PatrickOrjieh/life-sync/Sprint_1/Optiband.pptx

## Optiband

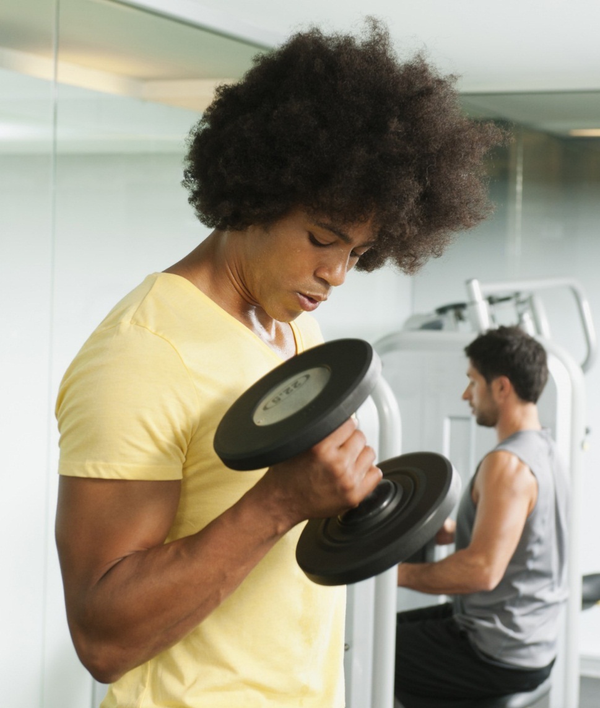
[picture p24: figure]
Two people lifting weights
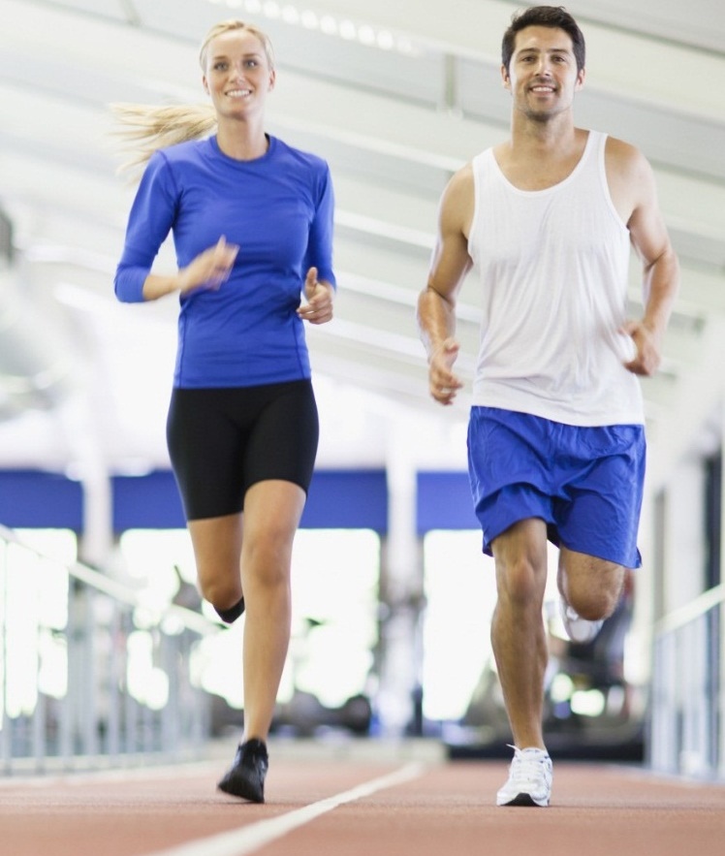
[picture p25: figure]
Man and woman running on indoor track

By LifeSync

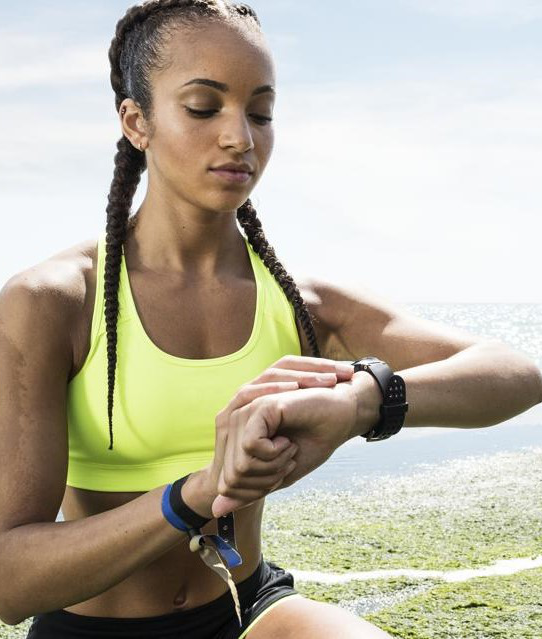
[picture p26: figure]

## Project Scope

- Develop a wearable fitness tracker
- Aid in achievement of optimal exercise
- Monitor user stats to provide guidance
- Avoidance of overexertion
- For teenagers/young adults new to the gym

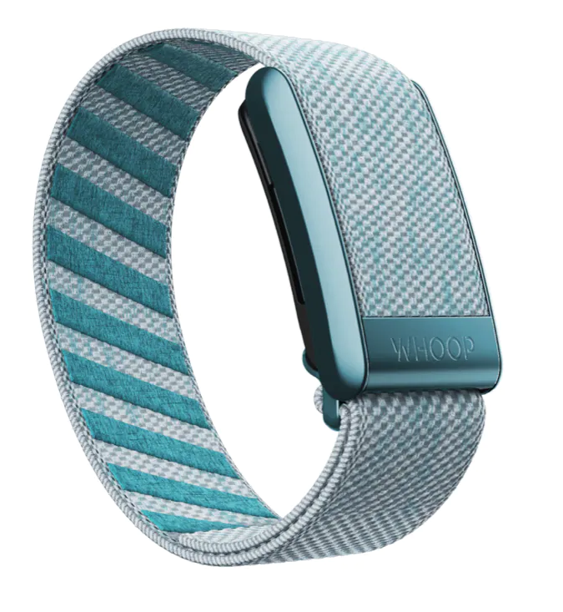
[picture p27: figure]

## Hardware Overview

- Insert Hardware info here

## Functional & Non-functional Requirements

Functional:
- Heart rate and Oxygen Saturation monitoring
- User Data Input
- Real-Time Feedback
- Workout Duration Timer
- Connectivity with Mobile App

Non-Functional:
Usability
Battery Life
Durability & build
Data security & privacy
Responsiveness

## U/T/S/E Analysis – Average user

- User – Some gym experience, uses technology regularly
- Task – engage in effective workouts without over exhaustion
- System – Valuable workout assistant & safety device
- Environment – Local gym, distractions: other gym-goers

## System Conceptual model design

- Hardware Components – Sensors, Bluetooth module, Battery
- Software Components – Mobile App, Account Management, Data Storage, Notifications
- User Experience – UI Design, User Feedback

## Thanks for listening!
