PatrickOrjieh/life-sync/Sprint_2/Amended Roles.docx

Roles

Robert - Team lead, Front-end Developer

Patrick - Back-end Developer, Database Management

Hannah – Hardware Management, Front-end Developer

Conor – UI Designer, Lead Tester
