PatrickOrjieh/life-sync/Sprint_0/Project-Role.docx

Project Manager Responsibilities: The Project Manager takes charge of overseeing the entire project from start to finish. To ensure that every task is in line with the project's goals, efficiently manage budgets, set timelines, and serve as the main point of contact for all stakeholders. Assigned to: Robert.

Scrum Master Responsibilities: The Scrum Master plays an important role in guiding the team through the Agile framework. To coordinate sprint planning sessions, lead daily hurdles, and review the outcomes of each sprint to ensure efficiency. Assigned to: It's a team effort - everyone is engaged.

Hardware Engineer Responsibilities: The Hardware Engineer explores the tangible aspects of the band. The focus is on picking out the right sensors, ensuring they function as intended, and communicating with other team members to integrate these components. Assigned to: Hannah.

Frontend Developer Responsibilities: The Frontend Developer crafts the visible parts of the apps linked with the band. The goal is to make sure it's not only responsive but also user-centric, and that it perfectly matches the vision laid out by the UI/UX designer. Assigned to: Robert.

UI/UX Designer Responsibilities: The UI/UX Designer is the creative force behind the project, tasked with sketching out user-friendly and attractive interfaces for the related apps. To ensure users have a hassle-free experience and work side by side with the Frontend Developer to make their designs a reality. Assigned to: Conor.

Backend and Database Developer Responsibilities: This role is all about the backbone of the application. The Backend and Database Developer ensures smooth communication between the server and frontend. Apart from that, design, roll out, and oversee the database, keeping eye on data safety and consistency. Assigned to: Patrick.

Tester (QA Engineer) Responsibilities: The Tester, or QA Engineer, is the last line of defense before the product reaches users. The duty is to identify any glitches, report them, and conduct tests on both the software and hardware parts. Work hand in hand with the developers to troubleshoot any found issues. Assigned to: Tom.
