PatrickOrjieh/life-sync/Sprint_3/UI Mockups/login page.jpg

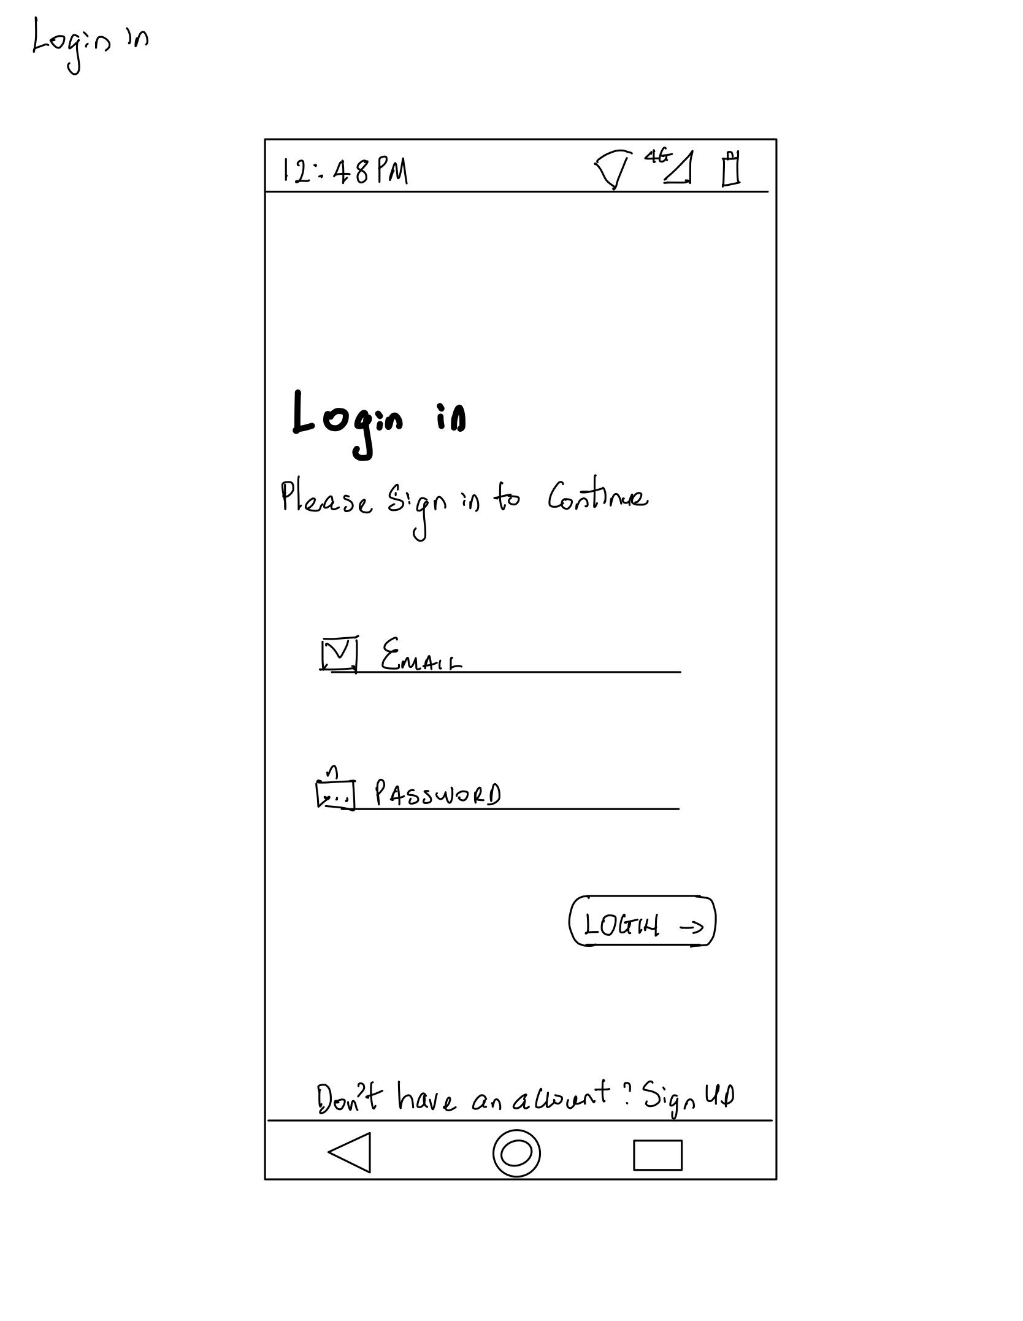
Sprint_3/UI Mockups/login page.jpg
