PatrickOrjieh/life-sync/Sprint_3/UI Mockups/main page.jpg

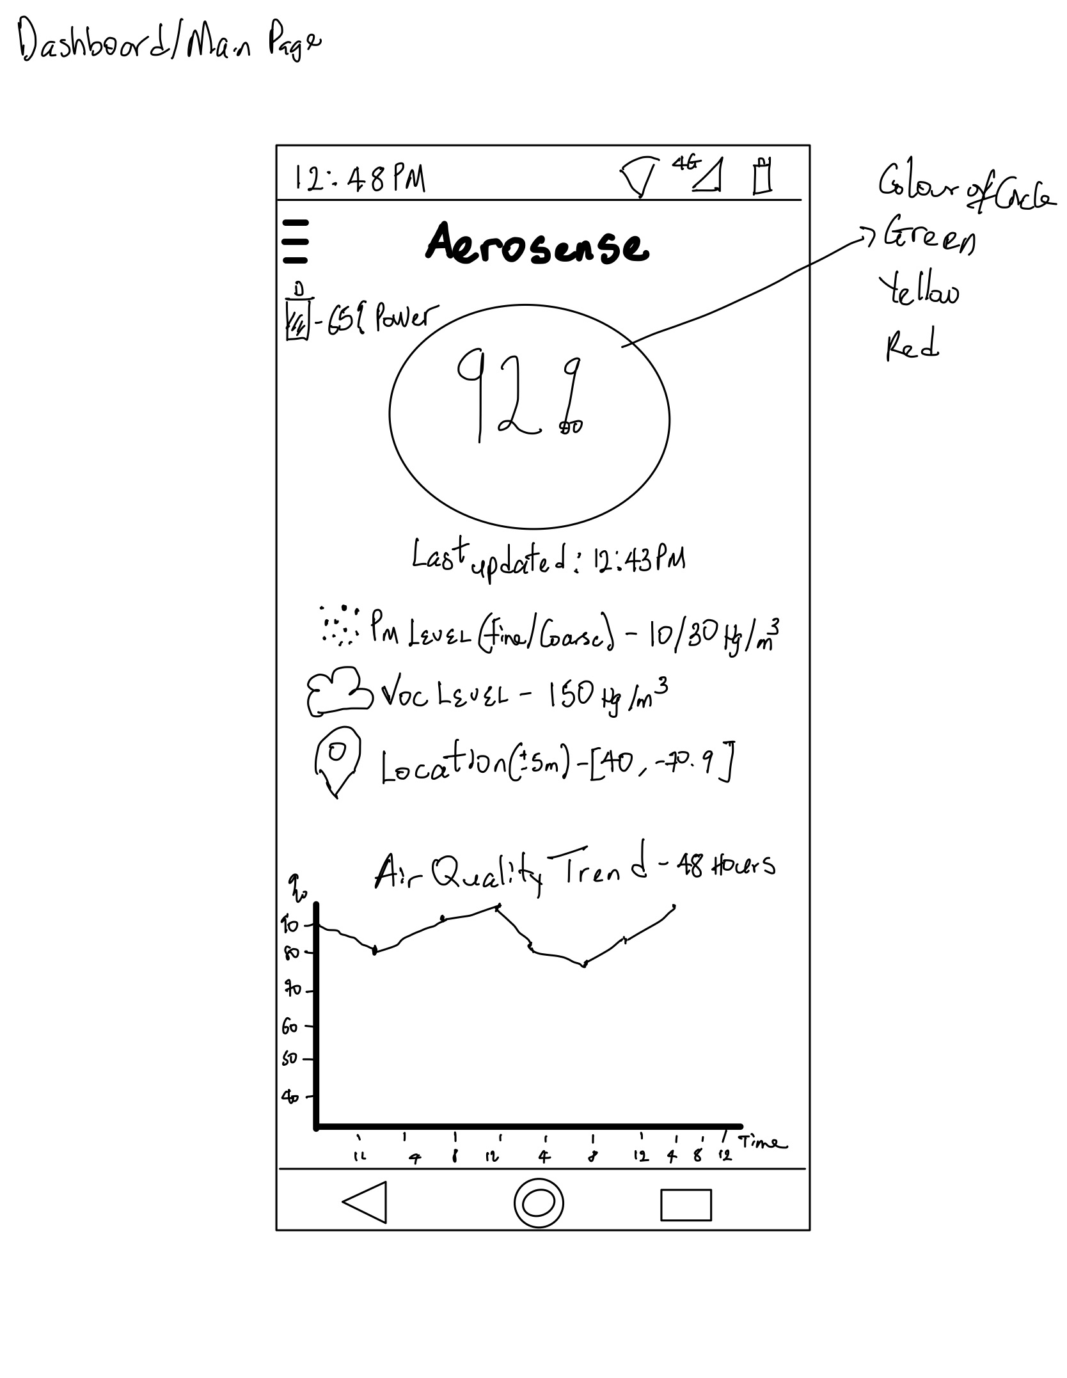
Sprint_3/UI Mockups/main page.jpg
