PatrickOrjieh/life-sync/Sprint_3/UI Mockups/menu screen.jpg

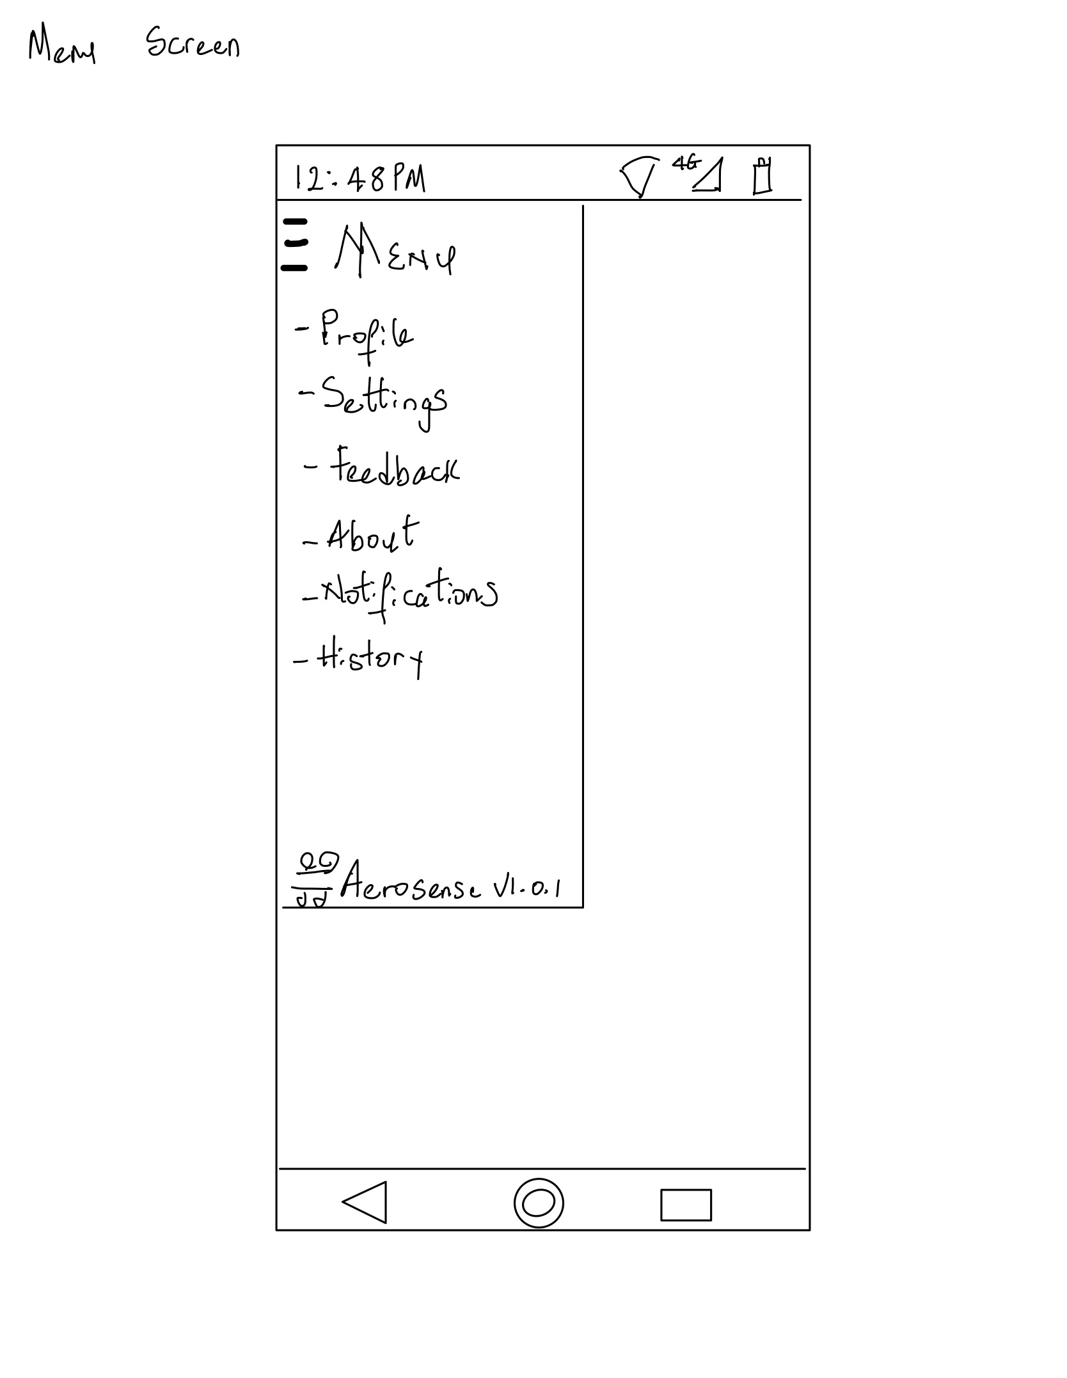
Sprint_3/UI Mockups/menu screen.jpg
