PatrickOrjieh/life-sync/Sprint_3/UI Mockups/notifications.jpg

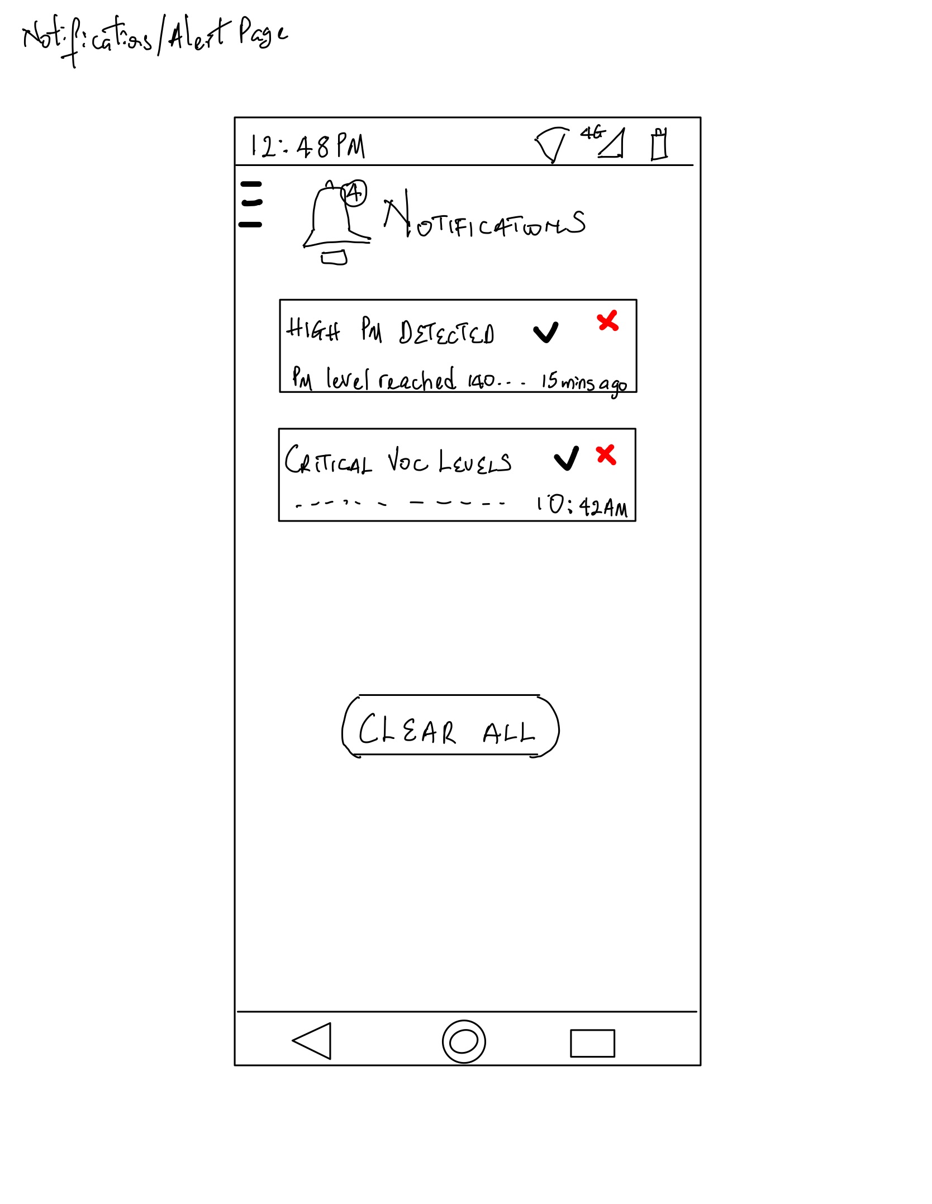
Sprint_3/UI Mockups/notifications.jpg
