PatrickOrjieh/life-sync/Sprint_3/UI Mockups/profile.jpg

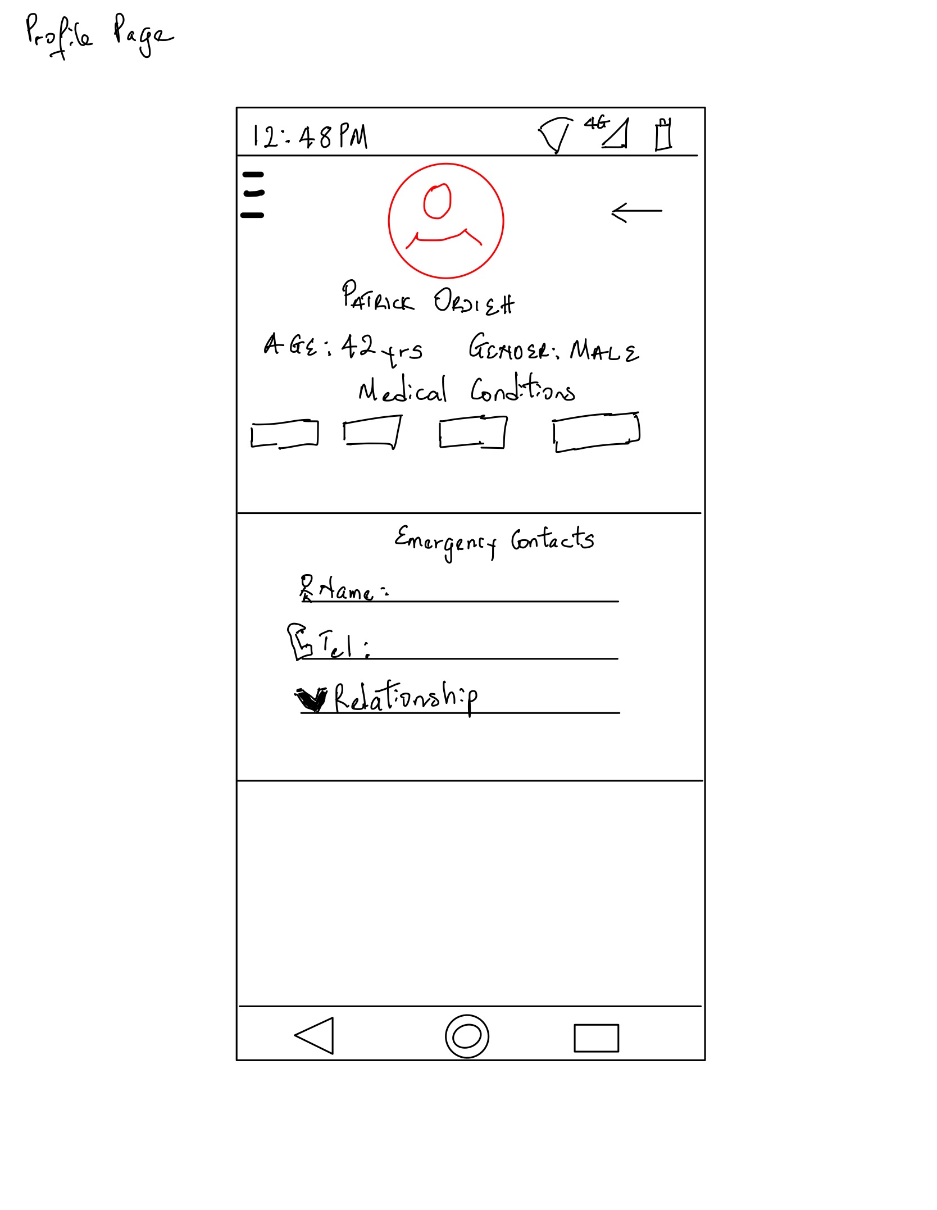
Sprint_3/UI Mockups/profile.jpg
