PatrickOrjieh/life-sync/Sprint_3/UI Mockups/register page.jpg

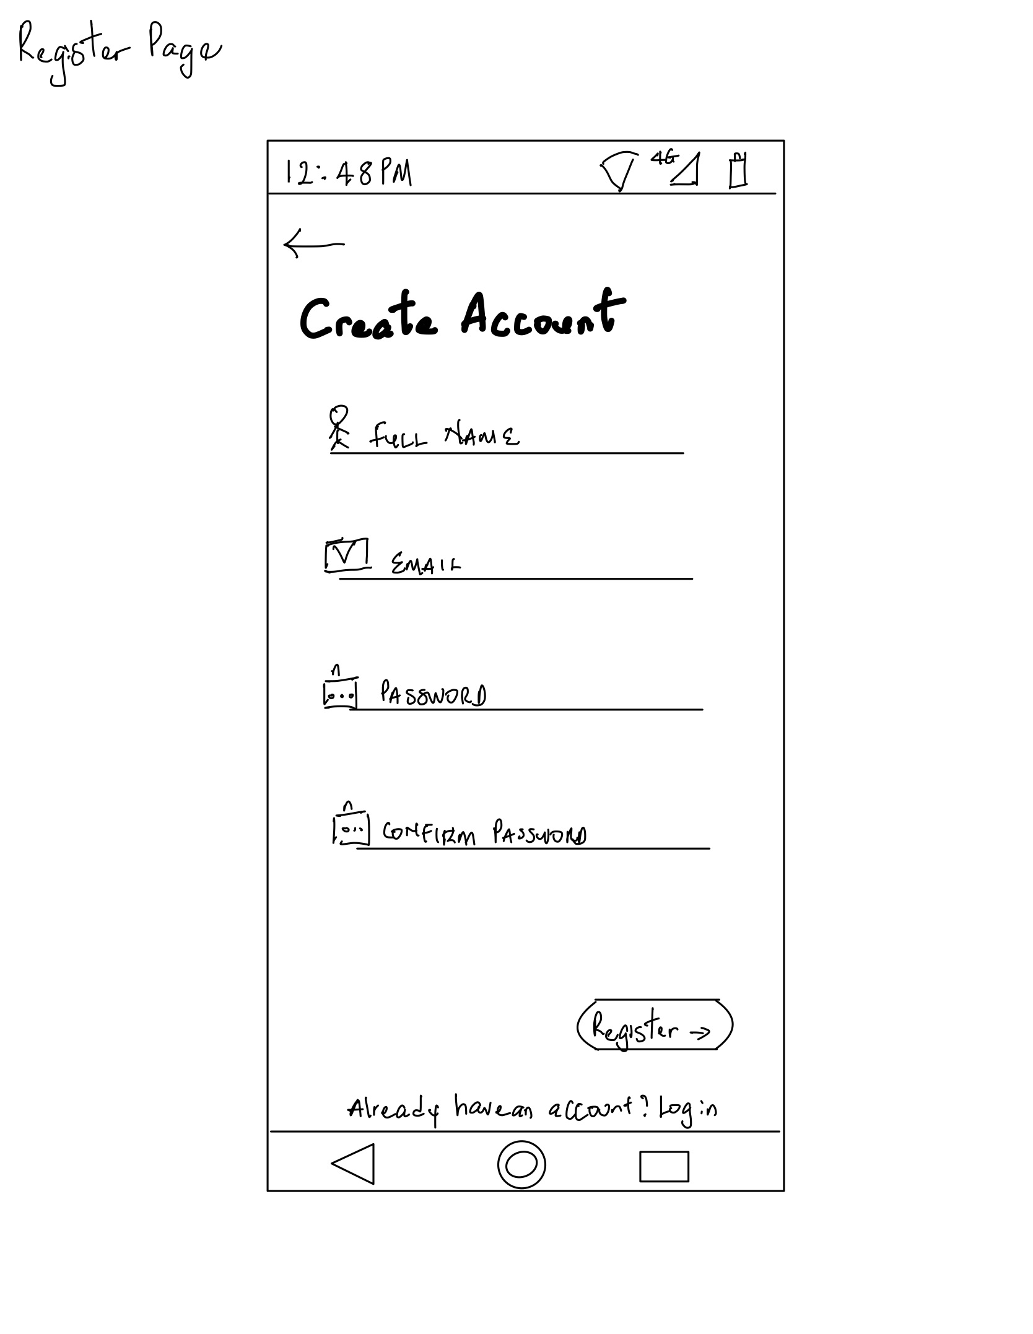
Sprint_3/UI Mockups/register page.jpg
