PatrickOrjieh/life-sync/Sprint_3/UI Mockups/settings screen.jpg

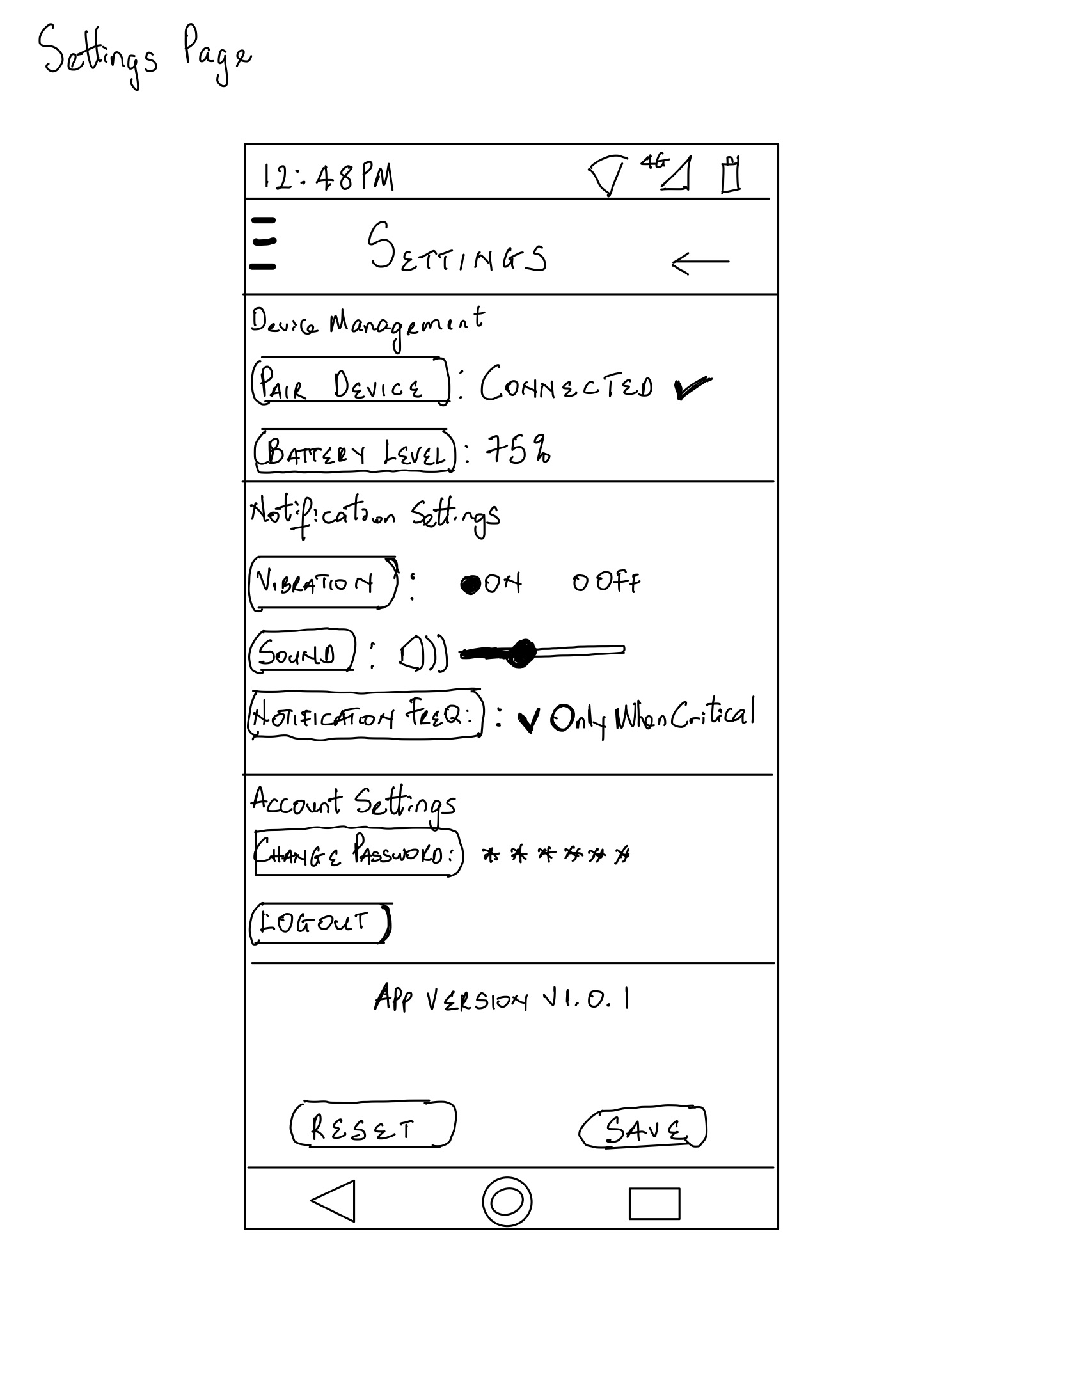
Sprint_3/UI Mockups/settings screen.jpg
