PatrickOrjieh/life-sync/Sprint_4/Database ERD Diagram.png

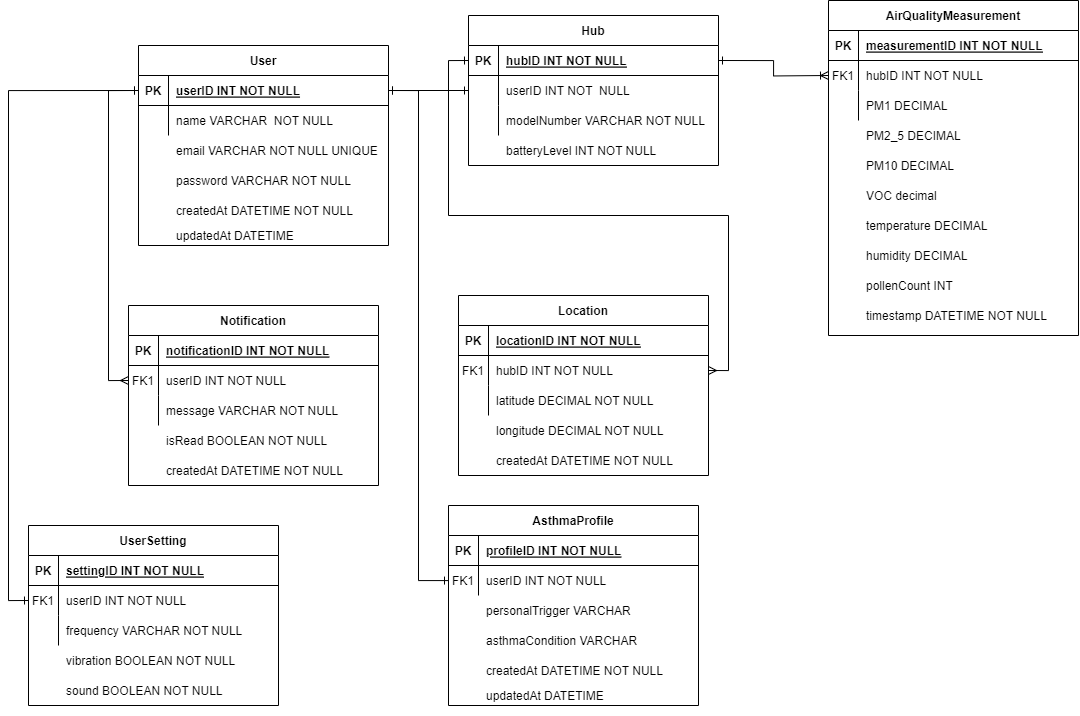
Sprint_4/Database ERD Diagram.png
