PatrickOrjieh/life-sync/Sprint_4/Paper Prototype/Hamburger_Menu.png

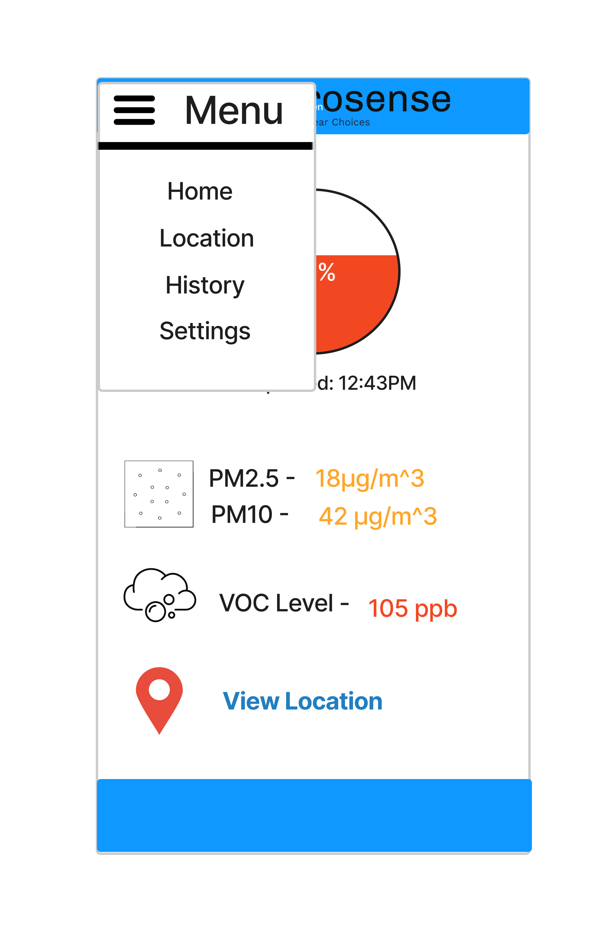
Sprint_4/Paper Prototype/Hamburger_Menu.png
