PatrickOrjieh/life-sync/Sprint_3/UI Mockups/history.jpg

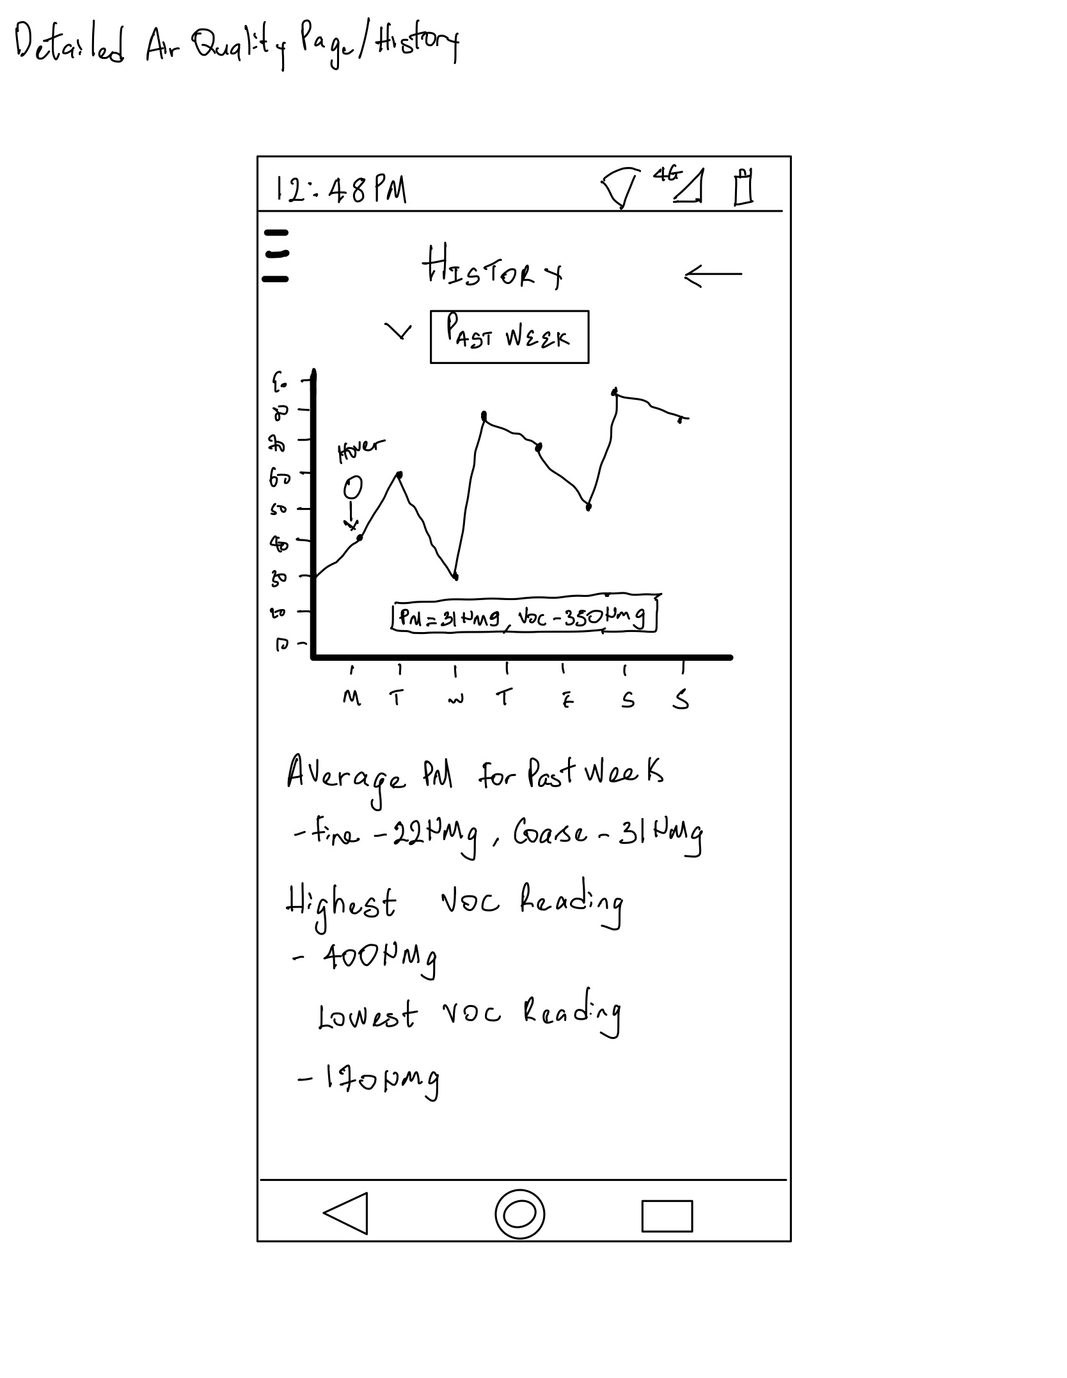
Sprint_3/UI Mockups/history.jpg
