PatrickOrjieh/life-sync/Sprint_4/Paper Prototype/History.png

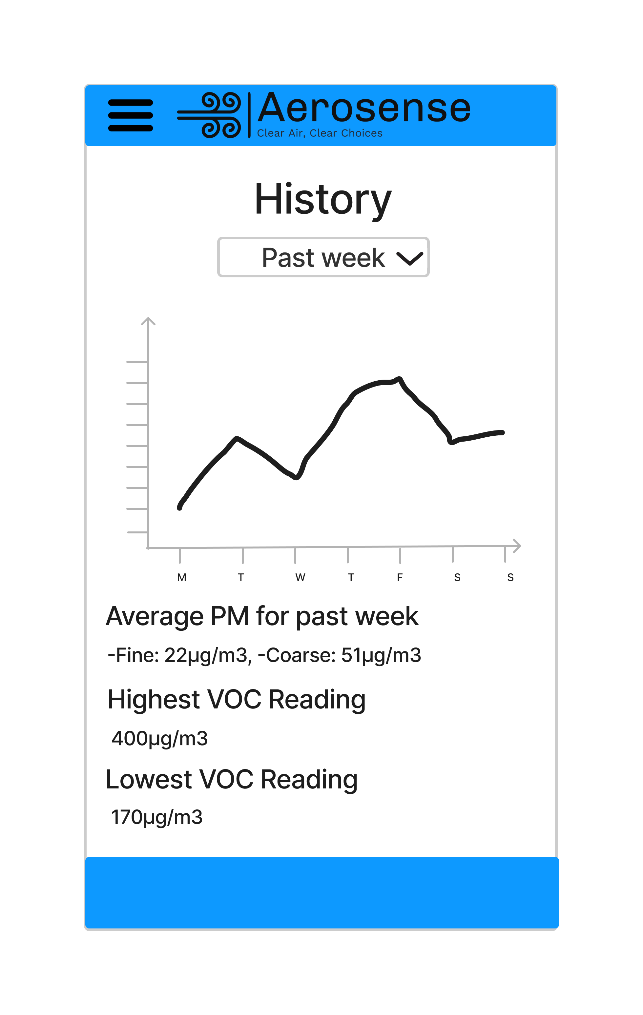
Sprint_4/Paper Prototype/History.png
